IvkoPivko/ivee/Images and CADs/01.jpg

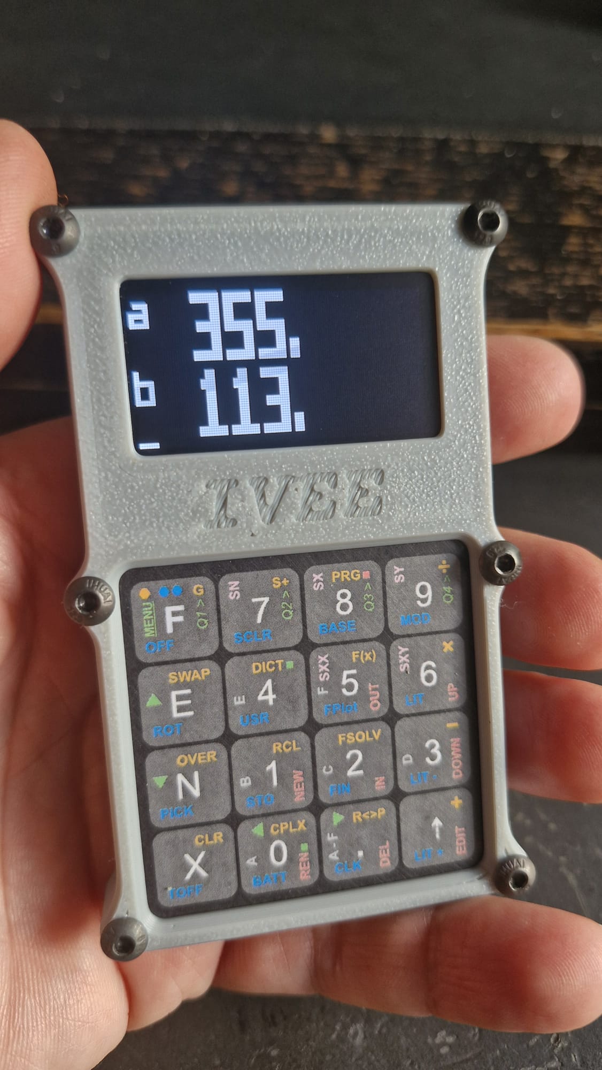
Images and CADs/01.jpg
