IvkoPivko/ivee/Images and CADs/02.jpg

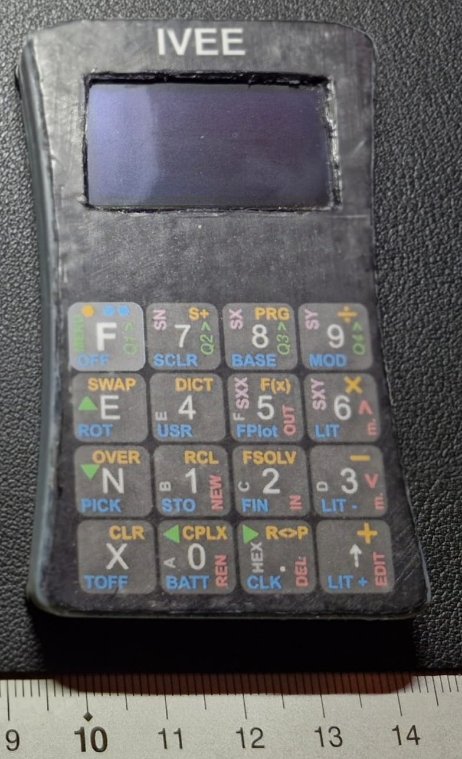
Images and CADs/02.jpg
