IvkoPivko/ivee/Images and CADs/03.jpg

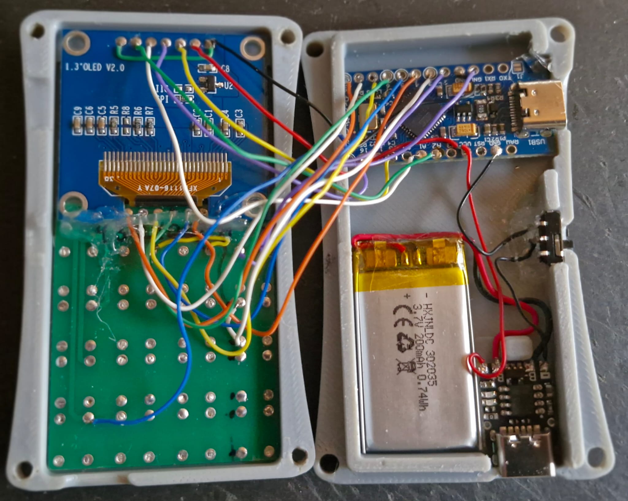
Images and CADs/03.jpg
